Computacao-Fisica-UFSJ/projeto-final-mesmo-robo-desviador-de-paredes/imagem_componentes/dimmer_2000W.webp

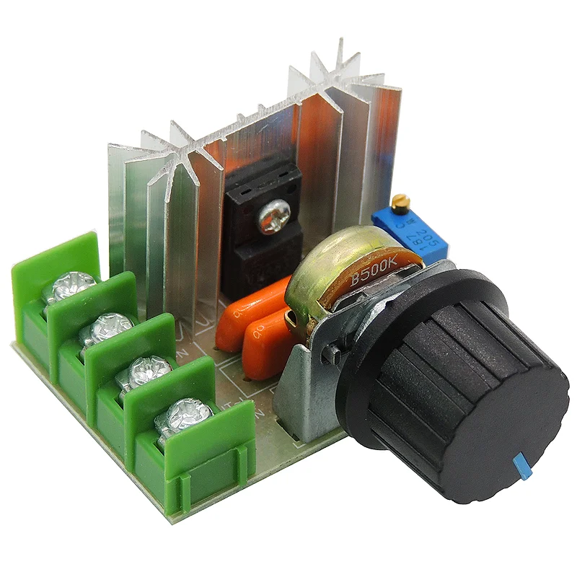
imagem_componentes/dimmer_2000W.webp
