Computacao-Fisica-UFSJ/projeto-final-mesmo-robo-desviador-de-paredes/imagem_componentes/sensor-de-nivel-de-agua-para-arduino-fd10.jpg

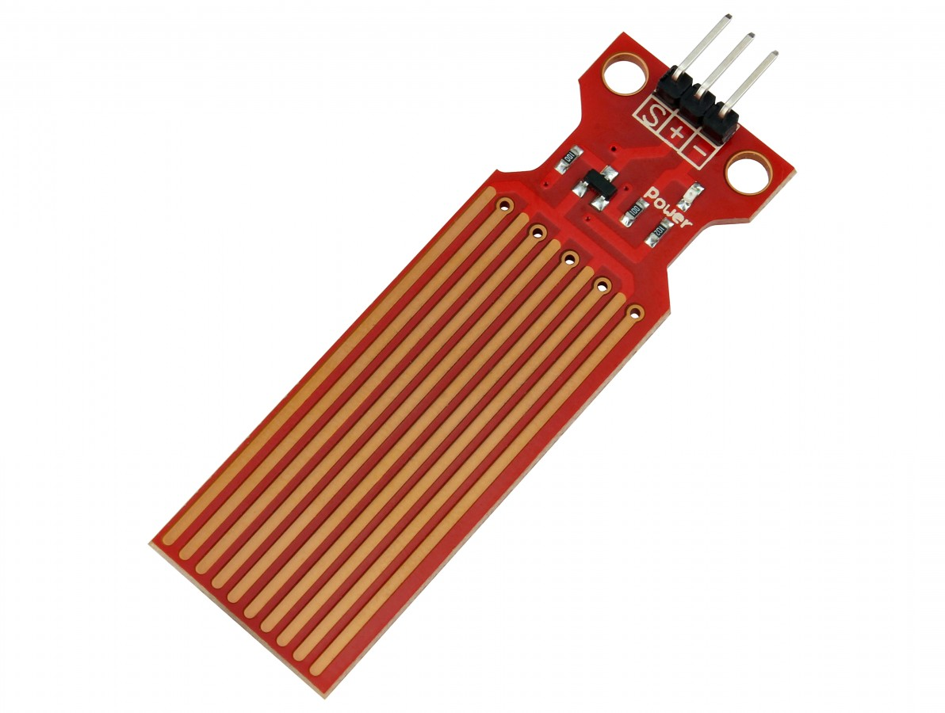
imagem_componentes/sensor-de-nivel-de-agua-para-arduino-fd10.jpg
